emsec/ChameleonMini/RevE/Software/img/screenshot.png

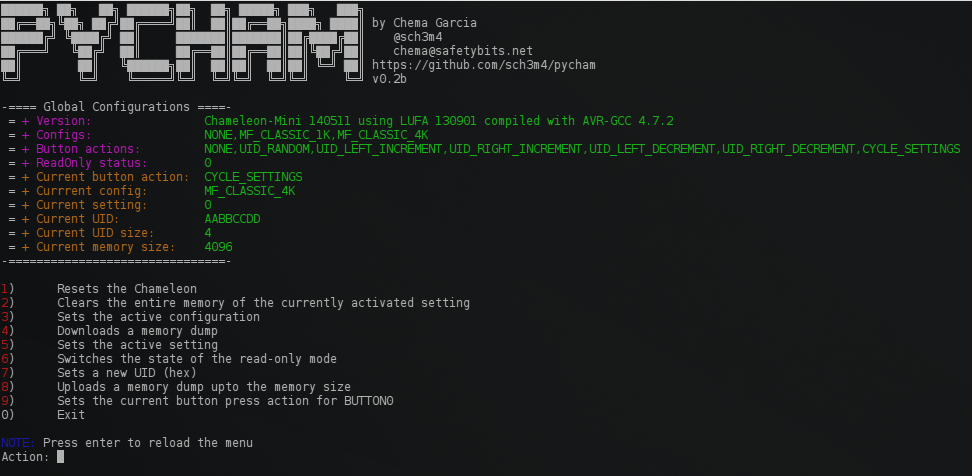
RevE/Software/img/screenshot.png
